sanworks/Frame2TTL/Firmware/Frame2TTL/ArCOM.cpp

/*
----------------------------------------------------------------------------

This file is part of the Sanworks ArCOM repository
Copyright (C) 2016 Sanworks LLC, Sound Beach, New York, USA

----------------------------------------------------------------------------

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
*/
#include <Arduino.h>
#include "ArCOM.h"

ArCOM::ArCOM(Stream &s) {
  ArCOMstream = &s;  // Sets the interface (Serial, Serial1, SerialUSB, etc.)
}
unsigned int ArCOM::available() {
  return ArCOMstream->available();
}
void ArCOM::flush() {
  ArCOMstream->flush();
}
void ArCOM::writeByte(byte byte2Write) {
  ArCOMstream->write(byte2Write);
}
void ArCOM::writeUint8(byte byte2Write) {
  ArCOMstream->write(byte2Write);
}
void ArCOM::writeChar(char char2Write) {
  ArCOMstream->write(char2Write);
}
void ArCOM::writeUint16(uint16_t int2Write) {
    typeBuffer.uint16 = int2Write;
    ArCOMstream->write(typeBuffer.byteArray, 2);
}
void ArCOM::writeUint32(uint32_t int2Write) {
    typeBuffer.uint32 = int2Write;
    ArCOMstream->write(typeBuffer.byteArray, 4);
}
byte ArCOM::readByte(){
  while (ArCOMstream->available() == 0) {}
  return ArCOMstream->read();
}
byte ArCOM::readUint8(){
  while (ArCOMstream->available() == 0) {}
  return ArCOMstream->read();
}
char ArCOM::readChar(){
  while (ArCOMstream->available() == 0) {}
  return ArCOMstream->read();
}
unsigned short ArCOM::readUint16() {
  while (ArCOMstream->available() == 0) {}
  typeBuffer.byteArray[0] = ArCOMstream->read();
  while (ArCOMstream->available() == 0) {}
  typeBuffer.byteArray[1] = ArCOMstream->read();
  return typeBuffer.uint16;
}

unsigned long ArCOM::readUint32() {
  while (ArCOMstream->available() == 0) {}
  typeBuffer.byteArray[0] = ArCOMstream->read();
  while (ArCOMstream->available() == 0) {}
  typeBuffer.byteArray[1] = ArCOMstream->read();
  while (ArCOMstream->available() == 0) {}
  typeBuffer.byteArray[2] = ArCOMstream->read();
  while (ArCOMstream->available() == 0) {}
  typeBuffer.byteArray[3] = ArCOMstream->read();
  return typeBuffer.uint32;
}

void ArCOM::writeInt8(int8_t int2Write) {
  typeBuffer.int8 = int2Write;
  ArCOMstream->write(typeBuffer.byteArray[0]);
}

void ArCOM::writeInt16(int16_t int2Write) {
  typeBuffer.int16 = int2Write;
  ArCOMstream->write(typeBuffer.byteArray[0]);
  ArCOMstream->write(typeBuffer.byteArray[1]);
}

void ArCOM::writeInt32(int32_t int2Write) {
  typeBuffer.int32 = int2Write;
  ArCOMstream->write(typeBuffer.byteArray[0]);
  ArCOMstream->write(typeBuffer.byteArray[1]);
  ArCOMstream->write(typeBuffer.byteArray[2]);
  ArCOMstream->write(typeBuffer.byteArray[3]);
}

int8_t ArCOM::readInt8() {
  while (ArCOMstream->available() == 0) {}
  typeBuffer.byteArray[0] = ArCOMstream->read();
  return typeBuffer.int8;
}
int16_t ArCOM::readInt16() {
  while (ArCOMstream->available() == 0) {}
  typeBuffer.byteArray[0] = ArCOMstream->read();
  while (ArCOMstream->available() == 0) {}
  typeBuffer.byteArray[1] = ArCOMstream->read();
  return typeBuffer.int16;
}
int32_t ArCOM::readInt32() {
  while (ArCOMstream->available() == 0) {}
  typeBuffer.byteArray[0] = ArCOMstream->read();
  while (ArCOMstream->available() == 0) {}
  typeBuffer.byteArray[1] = ArCOMstream->read();
  while (ArCOMstream->available() == 0) {}
  typeBuffer.byteArray[2] = ArCOMstream->read();
  while (ArCOMstream->available() == 0) {}
  typeBuffer.byteArray[3] = ArCOMstream->read();
  return typeBuffer.int32;
}
void ArCOM::writeByteArray(byte numArray[], unsigned int nValues) {
  ArCOMstream->write(numArray, nValues);
}
void ArCOM::writeUint8Array(byte numArray[], unsigned int nValues) {
  ArCOMstream->write(numArray, nValues);
}
void ArCOM::writeCharArray(char charArray[], unsigned int nValues) {
  ArCOMstream->write(charArray, nValues);
}
void ArCOM::writeInt8Array(int8_t numArray[], unsigned int nValues) {
  for (int i = 0; i < nValues; i++) {
    typeBuffer.int8 = numArray[i];
    ArCOMstream->write(typeBuffer.byteArray[0]);
  }
}
void ArCOM::writeUint16Array(unsigned short numArray[], unsigned int nValues) {
  for (unsigned int i = 0; i < nValues; i++) {
    typeBuffer.uint16 = numArray[i];
    ArCOMstream->write(typeBuffer.byteArray, 2);
  }
}
void ArCOM::writeInt16Array(int16_t numArray[], unsigned int nValues) {
  for (int i = 0; i < nValues; i++) {
    typeBuffer.int16 = numArray[i];
    ArCOMstream->write(typeBuffer.byteArray, 2);
  }
}
void ArCOM::writeUint32Array(unsigned long numArray[], unsigned int nValues) {
  for (unsigned int i = 0; i < nValues; i++) {
    typeBuffer.uint32 = numArray[i];
      ArCOMstream->write(typeBuffer.byteArray, 4);
  }
}
void ArCOM::writeInt32Array(long numArray[], unsigned int nValues) {
  for (unsigned int i = 0; i < nValues; i++) {
    typeBuffer.int32 = numArray[i];
      ArCOMstream->write(typeBuffer.byteArray, 4);
  }
}
void ArCOM::readByteArray(byte numArray[], unsigned int nValues) {
  ArCOMstream->readBytes(numArray, nValues);
}
void ArCOM::readUint8Array(byte numArray[], unsigned int nValues) {
  ArCOMstream->readBytes(numArray, nValues);
}
void ArCOM::readCharArray(char charArray[], unsigned int nValues) {
    ArCOMstream->readBytes(charArray, nValues);
}
void ArCOM::readInt8Array(int8_t numArray[], unsigned int nValues) {
  for (unsigned int i = 0; i < nValues; i++) {
    while (ArCOMstream->available() == 0) {}
    typeBuffer.byteArray[0] = ArCOMstream->read();
    numArray[i] = typeBuffer.int8;
  }
}
void ArCOM::readUint16Array(unsigned short numArray[], unsigned int nValues) {
  for (unsigned int i = 0; i < nValues; i++) {
    ArCOMstream->readBytes(typeBuffer.byteArray, 2);
    numArray[i] = typeBuffer.uint16;
  }
}
void ArCOM::readInt16Array(short numArray[], unsigned int nValues) {
  for (unsigned int i = 0; i < nValues; i++) {
    ArCOMstream->readBytes(typeBuffer.byteArray, 2);
    numArray[i] = typeBuffer.int16;
  }
}
void ArCOM::readUint32Array(unsigned long numArray[], unsigned int nValues) {
  for (unsigned int i = 0; i < nValues; i++) {
    ArCOMstream->readBytes(typeBuffer.byteArray, 4);
    numArray[i] = typeBuffer.uint32;
  }
}
void ArCOM::readInt32Array(long numArray[], unsigned int nValues) {
  for (unsigned int i = 0; i < nValues; i++) {
    ArCOMstream->readBytes(typeBuffer.byteArray, 4);
    numArray[i] = typeBuffer.int32;
  }
}
