sanworks/Frame2TTL/Software/Python/arcom.py

"""
----------------------------------------------------------------------------

This file is part of the Sanworks Frame2TTL repository
Copyright (C) Sanworks LLC, Rochester, New York, USA

----------------------------------------------------------------------------

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
# ArCOM (Arduino Communication) wraps PySerial and numpy to streamline communication of numpy arrays to and from Arduino
# A matching class for Arduino is provided in the ArCOM repository: https://github.com/sanworks/ArCOM

import numpy as np
import serial


class ArCom(object):
    def __init__(self, serial_port_name, baud_rate):
        self.typeNames = ('uint8', 'int8', 'char', 'uint16', 'int16', 'uint32', 'int32', 'single', 'double')
        self.typeBytes = (1, 1, 1, 2, 2, 4, 4, 8)
        self.serialObject = serial.Serial(serial_port_name, baud_rate, timeout=10, rtscts=True)

    def close(self):
        self.serialObject.close()

    def bytes_available(self):
        return self.serialObject.inWaiting()

    def write(self, *arg):  # Write to Arduino
        n_types = int(len(arg)/2)
        arg_pos = 0
        message_bytes = b''
        for i in range(0, n_types):
            data = arg[arg_pos]
            arg_pos += 1
            datatype = arg[arg_pos]
            arg_pos += 1
            if (datatype in self.typeNames) is False:
                raise ArCOMError('Error: ' + datatype + ' is not a data type supported by ArCOM.')
            datatype_pos = self.typeNames.index(datatype)
            
            if type(data).__module__ == np.__name__:
                npdata = data.astype(datatype)
            else:
                npdata = np.array(data, dtype=datatype)
            message_bytes += npdata.tobytes()
        self.serialObject.write(message_bytes)

    def read(self, *arg):  # Read from Arduino
        num_types = int(len(arg)/2)
        arg_pos = 0
        outputs = []
        for i in range(0, num_types):
            num_values = arg[arg_pos]
            arg_pos += 1
            datatype = arg[arg_pos]
            if (datatype in self.typeNames) is False:
                raise ArCOMError('Error: ' + datatype + ' is not a data type supported by ArCOM.')
            arg_pos += 1
            type_index = self.typeNames.index(datatype)
            byte_width = self.typeBytes[type_index]
            n_bytes2read = num_values*byte_width
            message_bytes = self.serialObject.read(n_bytes2read)
            n_bytes_read = len(message_bytes)
            if n_bytes_read < n_bytes2read:
                raise ArCOMError('Error: serial port timed out. ' + str(n_bytes_read) +
                                 ' bytes read. Expected ' + str(n_bytes2read) + ' byte(s).')
            this_output = np.frombuffer(message_bytes, datatype)
            if num_values == 1:  # Only return an array if returning more than 1 element
                this_output = this_output[0]
            outputs.append(this_output)
        if num_types == 1:
            outputs = this_output
        return outputs

    def __del__(self):
        self.serialObject.close()


class ArCOMError(Exception):
    pass
