sanworks/Frame2TTL/Python/v2/ArCOM_F2TTL.py

'''
----------------------------------------------------------------------------

This file is part of the Sanworks ArCOM repository
Copyright (C) 2021 Sanworks LLC, Rochester, New York, USA

----------------------------------------------------------------------------

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
You should have received a copy of the GNU General Public License
along with this program.  If not, see <http://www.gnu.org/licenses/>.
'''
import numpy as np
import serial

class ArCOM(object):
    def __init__(self, serialPortName, baudRate):
        self.serialObject = 0
        self.typeNames = ('uint8', 'int8', 'char', 'uint16', 'int16', 'uint32', 'int32', 'single')
        self.typeBytes = (1, 1, 1, 2, 2, 4, 4)
        self.typeSymbols = ('B', 'b', 'c', 'H', 'h', 'L', 'l')
        self.serialObject = serial.Serial(serialPortName, timeout=10, rtscts=True)
    def open(self, serialPortName, baudRate):
        self.serialObject = serial.Serial(serialPortName, baudRate, timeout=10)
    def close(self):
        self.serialObject.close()
    def bytesAvailable(self):
        return self.serialObject.inWaiting()
    def write(self,*arg):
        nTypes = int(len(arg)/2)
        argPos = 0;
        messageBytes = b''
        for i in range(0,nTypes):
            data = arg[argPos]
            argPos+= 1
            datatype = arg[argPos]
            argPos+= 1
            if ((datatype in self.typeNames) is False):
                raise ArCOMError('Error: ' + datatype + ' is not a data type supported by ArCOM.')
            datatypePos = self.typeNames.index(datatype)
            
            if type(data).__module__ == np.__name__:
                NPdata = data.astype(datatype)
            else:
                NPdata = np.array(data, dtype=datatype)
            messageBytes += NPdata.tobytes()               
        self.serialObject.write(messageBytes)
    def read(self,*arg): # Read an array of values
        nTypes = int(len(arg)/2);
        argPos = 0;
        outputs = [];
        for i in range(0,nTypes):
            nValues = arg[argPos]
            argPos+= 1
            datatype = arg[argPos]
            if ((datatype in self.typeNames) is False):
                raise ArCOMError('Error: ' + datatype + ' is not a data type supported by ArCOM.')
            argPos+= 1
            typeIndex = self.typeNames.index(datatype)
            byteWidth = self.typeBytes[typeIndex]
            nBytes2Read = nValues*byteWidth;
            messageBytes = self.serialObject.read(nBytes2Read)
            nBytesRead = len(messageBytes)
            if nBytesRead < nBytes2Read:
                raise ArCOMError('Error: serial port timed out. ' + str(nBytesRead) + ' bytes read. Expected ' + str(nBytes2Read) +' byte(s).')
            thisOutput = np.frombuffer(messageBytes, datatype)
            outputs.append(thisOutput)
        if nTypes == 1:
            outputs = thisOutput
        return outputs
    def __del__(self):
        self.serialObject.close()
class ArCOMError(Exception):
    pass
